samyarsadat/ROS-Remote/cad_files/solidworks_assets/parts/Generic_Power_Bank_Representation.SLDPRT

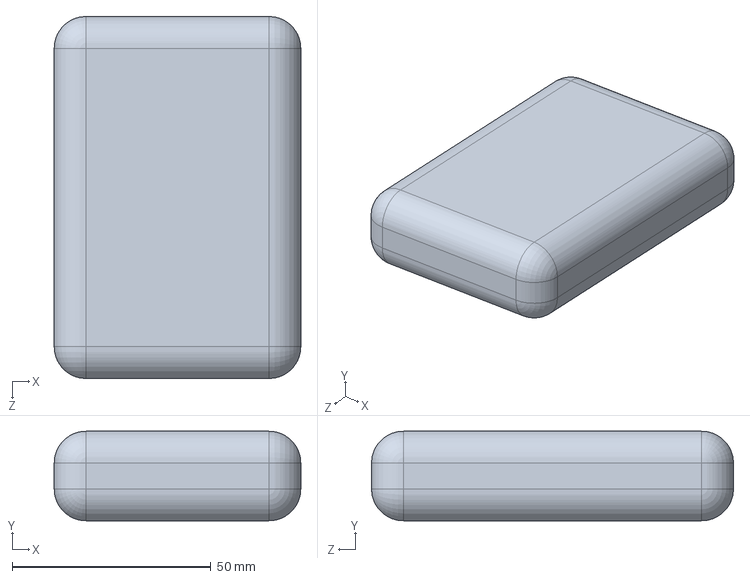
[picture p18: CAD file, 2026-08-17]
cad_files/solidworks_assets/parts/Generic_Power_Bank_Representation.SLDPRT
62.0 x 22.5 x 91.0 mm
