samyarsadat/ROS-Remote/cad_files/solidworks_assets/parts/40x60mm_protoboard.SLDPRT

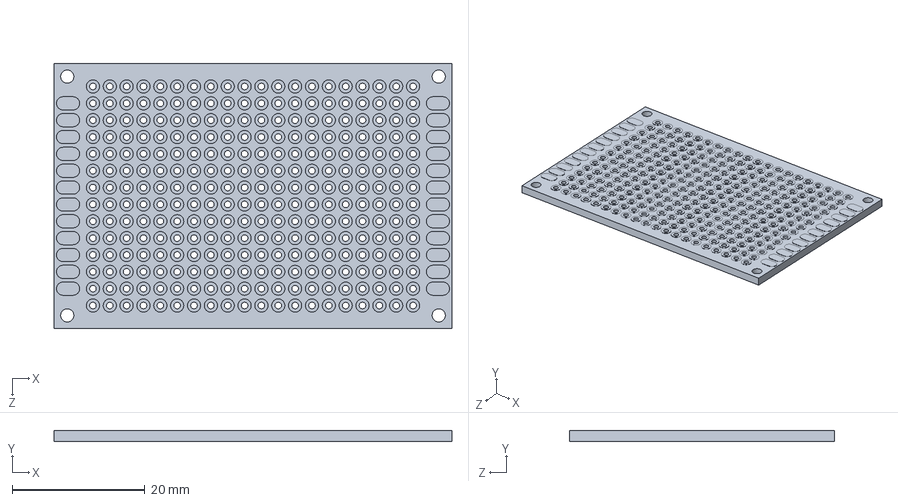
[picture p19: CAD file, 2026-08-17]
cad_files/solidworks_assets/parts/40x60mm_protoboard.SLDPRT
60.0 x 1.70 x 40.0 mm
