samyarsadat/ROS-Remote/cad_files/solidworks_assets/parts/Red_led.SLDPRT

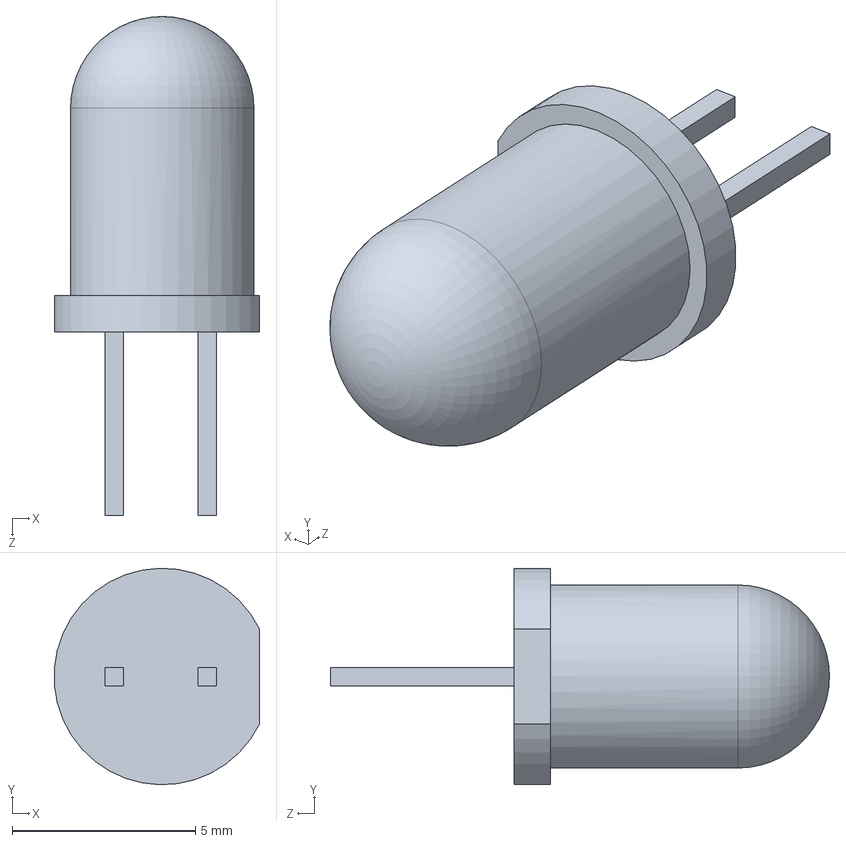
[picture p20: CAD file, 2026-08-17]
cad_files/solidworks_assets/parts/Red_led.SLDPRT
5.59 x 5.90 x 13.6 mm
