samyarsadat/ROS-Remote/cad_files/solidworks_assets/parts/7mm_Momentary_Button.SLDPRT

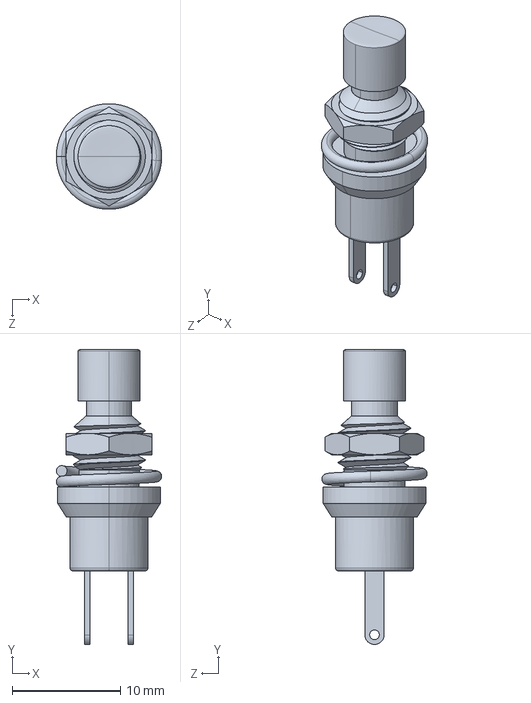
[picture p21: CAD file, 2026-08-17]
cad_files/solidworks_assets/parts/7mm_Momentary_Button.SLDPRT
9.76 x 27.3 x 9.76 mm
