samyarsadat/ROS-Remote/cad_files/solidworks_assets/parts/Raspberry_Pi_3.SLDPRT

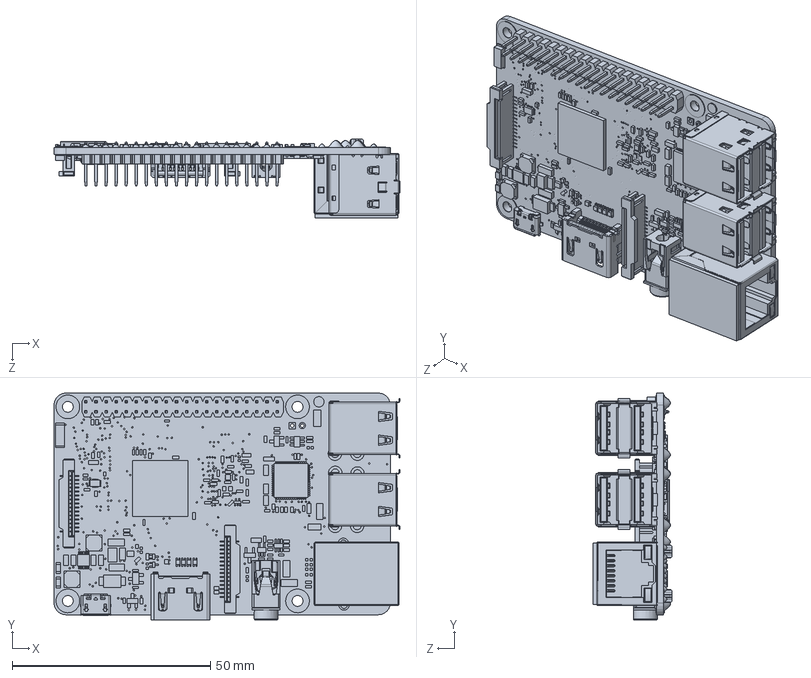
[picture p22: CAD file, 2026-08-17]
cad_files/solidworks_assets/parts/Raspberry_Pi_3.SLDPRT
87.4 x 57.3 x 19.9 mm
