samyarsadat/ROS-Remote/cad_files/solidworks_assets/parts/Potentiometer.sldprt

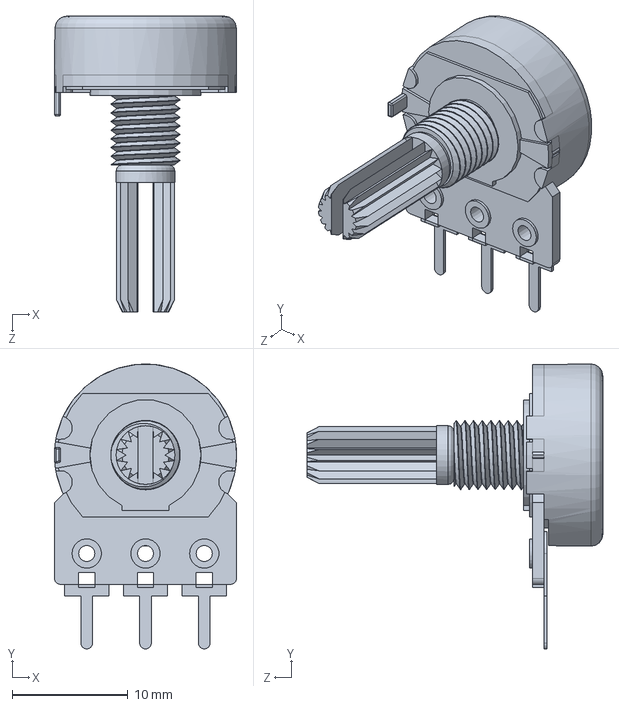
[picture p23: CAD file, 2026-08-17]
cad_files/solidworks_assets/parts/Potentiometer.sldprt
15.7 x 24.6 x 25.6 mm
