samyarsadat/ROS-Remote/cad_files/solidworks_assets/parts/M2.5_8.SLDPRT

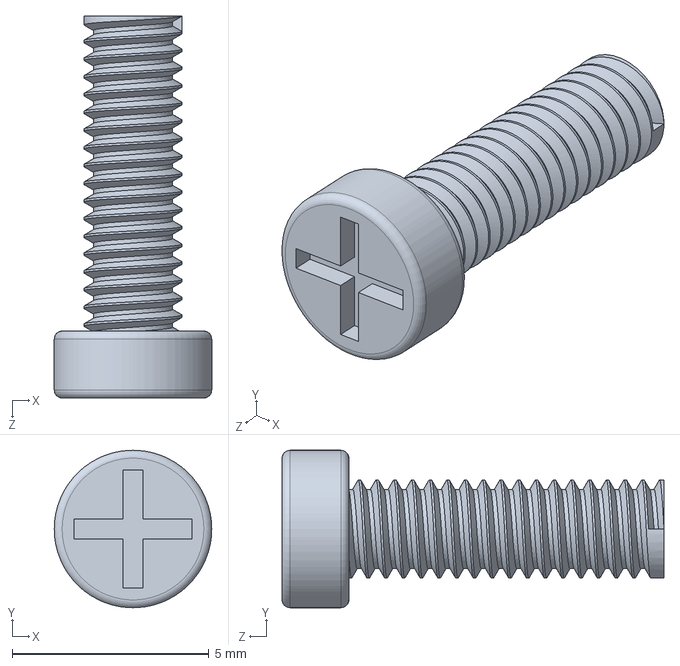
[picture p24: CAD file, 2026-08-17]
cad_files/solidworks_assets/parts/M2.5_8.SLDPRT
4.00 x 4.00 x 9.70 mm
