samyarsadat/ROS-Remote/cad_files/solidworks_assets/parts/16mm_e-stop_button.SLDPRT

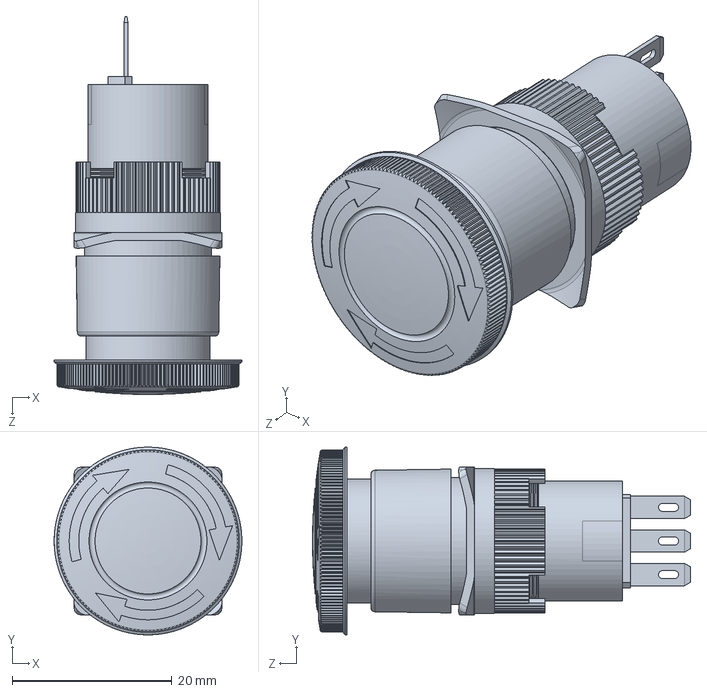
[picture p25: CAD file, 2026-08-17]
cad_files/solidworks_assets/parts/16mm_e-stop_button.SLDPRT
23.5 x 23.5 x 47.3 mm
