samyarsadat/ROS-Remote/cad_files/solidworks_assets/parts/Rotary_encoder_module.SLDPRT

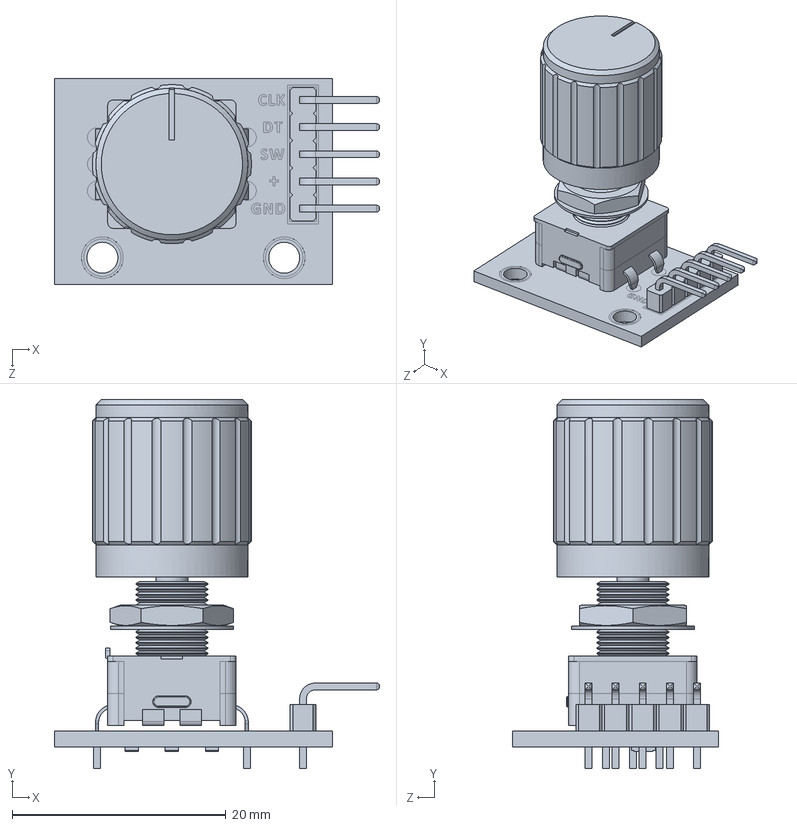
[picture p26: CAD file, 2026-08-17]
cad_files/solidworks_assets/parts/Rotary_encoder_module.SLDPRT
30.4 x 34.5 x 19.2 mm
