samyarsadat/ROS-Remote/cad_files/solidworks_assets/parts/20_pin_female_header_2.54mm.step

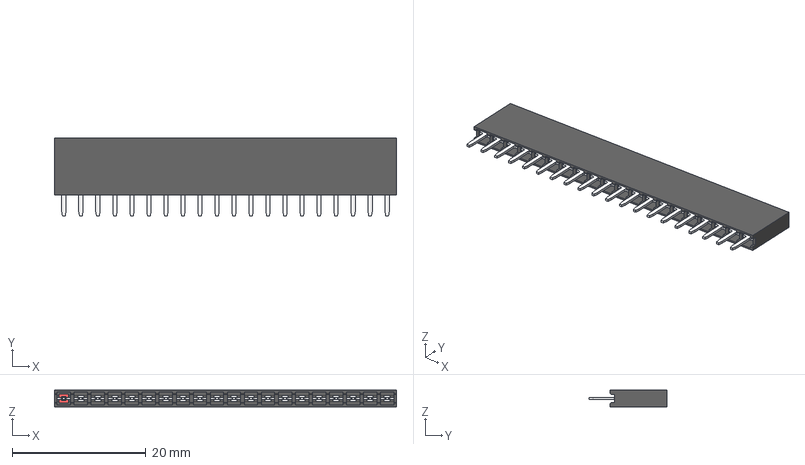
[picture p27: CAD file, 2024-07-23]
cad_files/solidworks_assets/parts/20_pin_female_header_2.54mm.step
51.0 x 11.7 x 2.50 mm
