samyarsadat/ROS-Remote/cad_files/solidworks_assets/parts/OM200A-M2_joystick.step

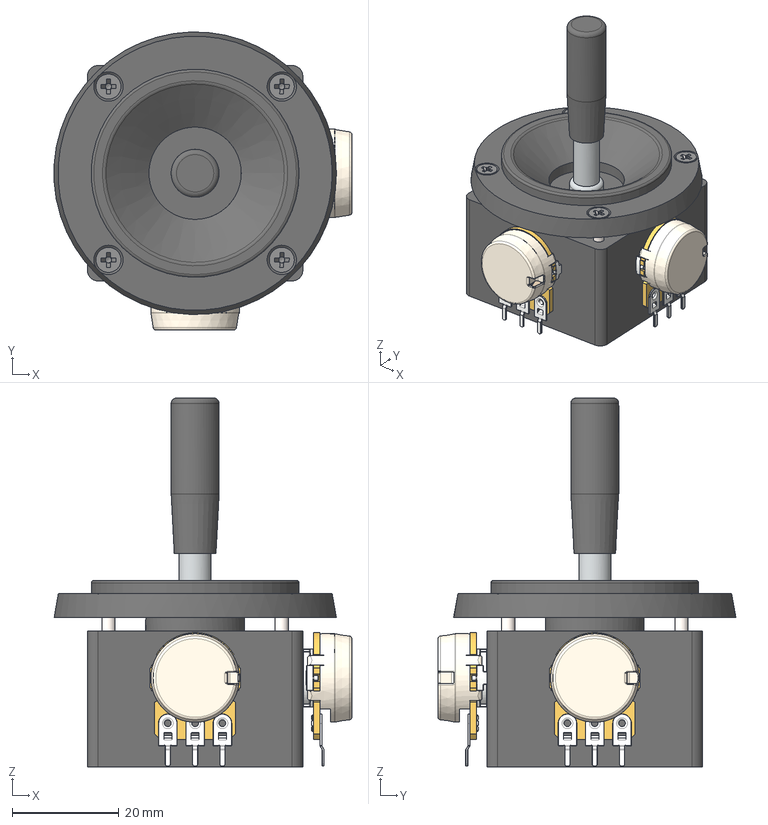
[picture p28: CAD file, 2024-07-23]
cad_files/solidworks_assets/parts/OM200A-M2_joystick.step
55.8 x 55.9 x 69.2 mm
Omter - 2 Axis potentiometer joystick without spring return OM200A-M2--1
pcb board x 2
base metal x 2
rotating rod metal x 2
pin1 x 6
sheild metal x 2
plastic base x 2
Mutter M7x075 x 2
Unterlegscheibe 11x7x0.5 x 2
Omter - 2 Axis potentiometer joystick without spring return OM200A-M2__
countersunk flat head cross recess screw_din x 4
