samyarsadat/ROS-Remote/cad_files/solidworks_assets/parts/12mm_key_operated_switch.step

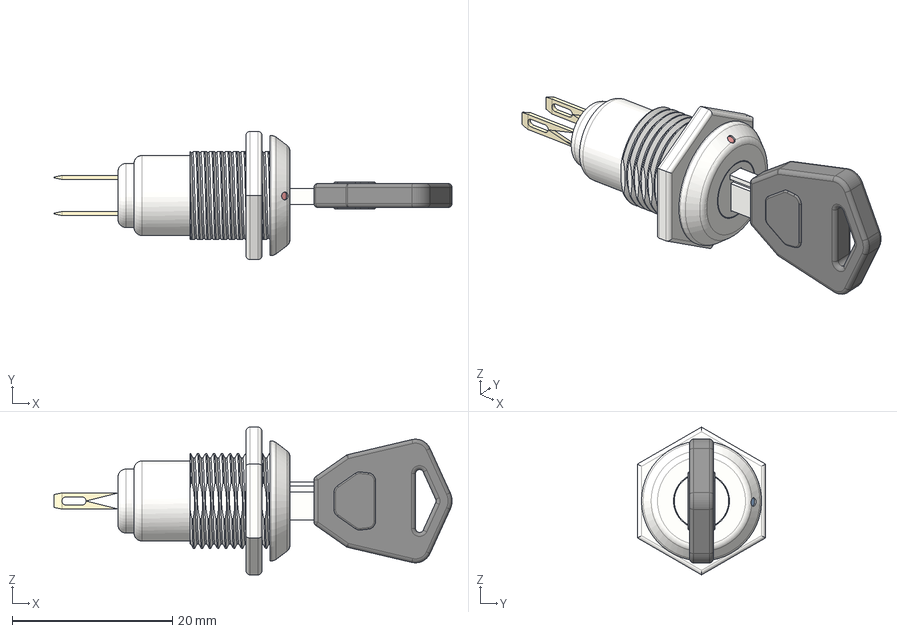
[picture p29: CAD file, 2024-07-23]
cad_files/solidworks_assets/parts/12mm_key_operated_switch.step
49.7 x 16.0 x 18.5 mm
