samyarsadat/ROS-Remote/cad_files/solidworks_assets/parts/20_pin_male_header_2.54mm.step

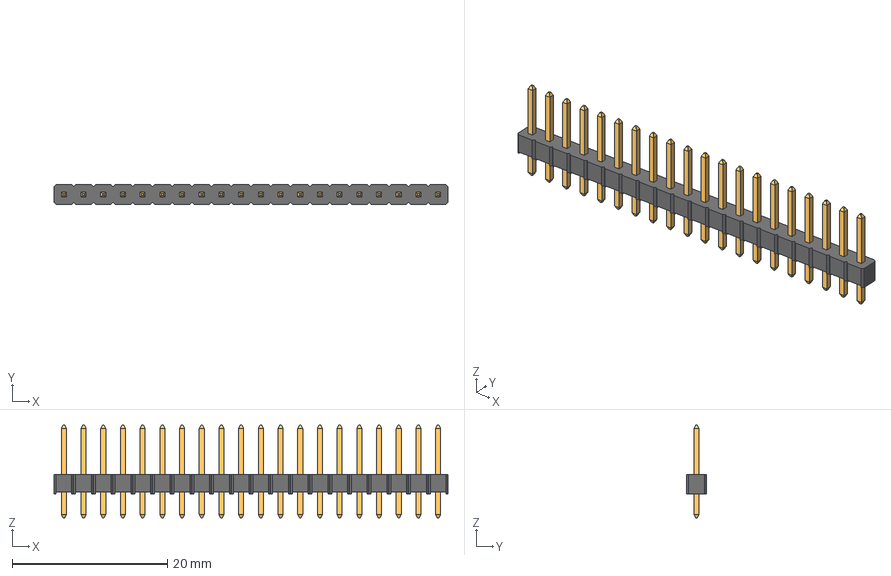
[picture p30: CAD file, 2024-07-23]
cad_files/solidworks_assets/parts/20_pin_male_header_2.54mm.step
50.8 x 2.54 x 11.9 mm
