samyarsadat/ROS-Remote/cad_files/solidworks_assets/parts/M2.5_20.SLDPRT

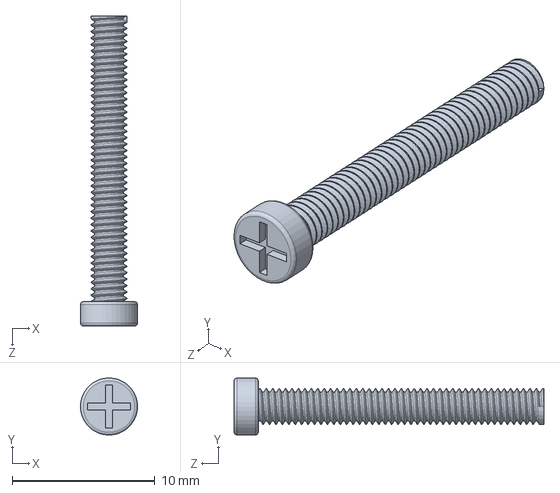
[picture p31: CAD file, 2024-07-19]
cad_files/solidworks_assets/parts/M2.5_20.SLDPRT
4.00 x 3.99 x 21.7 mm
