samyarsadat/ROS-Remote/cad_files/solidworks_assets/parts/Generic_DIN_7991.SLDPRT

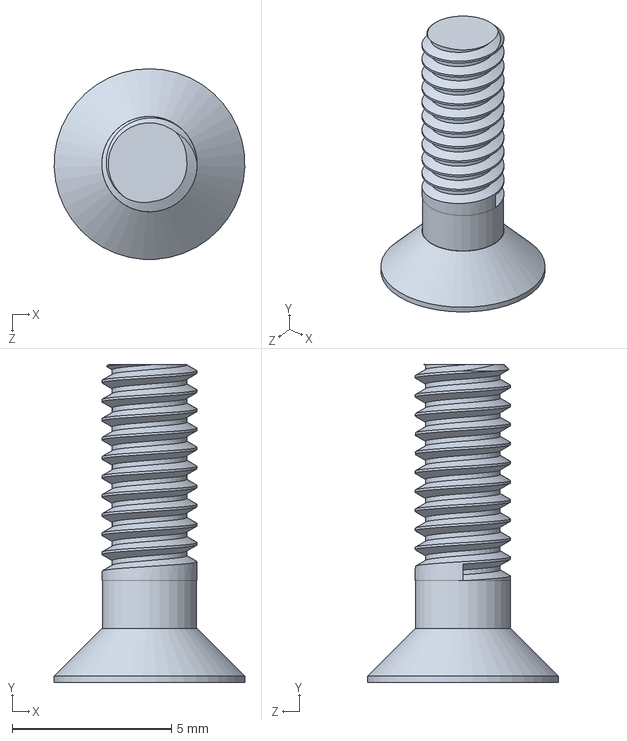
[picture p32: CAD file, 2024-07-19]
cad_files/solidworks_assets/parts/Generic_DIN_7991.SLDPRT
6.00 x 10.0 x 5.99 mm
