samyarsadat/ROS-Remote/cad_files/solidworks_assets/parts/Potentipmeter_knob.step

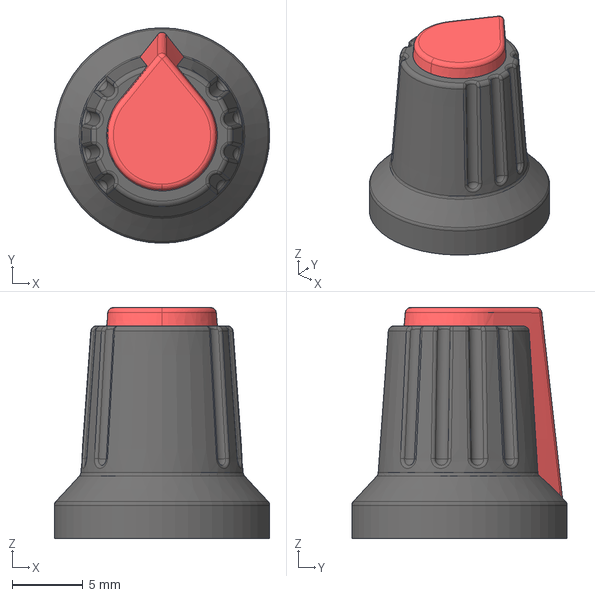
[picture p33: CAD file, 2024-07-19]
cad_files/solidworks_assets/parts/Potentipmeter_knob.step
15.2 x 15.2 x 16.3 mm
Rouge
Extérieur
