samyarsadat/ROS-Remote/source_code/ros_ws_remote/src/ros_remote_pui/ros_remote_pui/encoder_handler.py

#  The ROS remote project (PUI package)
#  Encoder IO handler. This is for GUI navigation using the encoder.
#  Copyright 2024 Samyar Sadat Akhavi
#  Written by Samyar Sadat Akhavi, 2024.
#
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
from PySide6.QtCore import QObject, Signal, QTimer, Slot
from PySide6.QtWidgets import QApplication, QPushButton, QTabBar, QCheckBox, QComboBox, QSlider, QWidget
from gpiozero import RotaryEncoder, Button
from ros_remote_gui.main_window import get_main_window
from ros_remote_pui.config import RpiIoConfig, ProgramConfig


# Encoder input handler
class EncoderInput(QObject):
    enc_rotated = Signal(bool)
    btn_pressed = Signal()

    def __init__(self):
        super().__init__()

        self._rotary_enc = RotaryEncoder(RpiIoConfig.ENCODER_PIN_A, RpiIoConfig.ENCODER_PIN_B)
        self._rotary_enc.when_rotated_clockwise = self._enc_rotate_call_cw
        self._rotary_enc.when_rotated_counter_clockwise = self._enc_rotate_call_ccw

        self._rotary_btn = Button(RpiIoConfig.ENCODER_BTN_PIN, pull_up=False, bounce_time=RpiIoConfig.BUTTON_DEBOUNCE_TIME_S)
        self._rotary_btn.when_activated = self._enc_btn_call

    def _enc_btn_call(self) -> None:
        self.btn_pressed.emit()

    def _enc_rotate_call_cw(self) -> None:
        self.enc_rotated.emit(True)

    def _enc_rotate_call_ccw(self) -> None:
        self.enc_rotated.emit(False)


# Encoder UI navigation handler
class EncoderNavHandler:
    def __init__(self):
        self._input_handler = EncoderInput()
        self._input_handler.enc_rotated.connect(self._enc_rotate)
        self._input_handler.btn_pressed.connect(self._enc_btn_press)

        self._highlight_timer = QTimer()
        self._highlight_timer.setInterval(ProgramConfig.ENCODER_HIGHLIGHT_TIMEOUT_MS)
        self._highlight_timer.setSingleShot(True)
        self._highlight_timer.timeout.connect(self._clear_highlight)

        self._highlight_stylesheet = "QWidget:focus { border: 1px solid blue; }"
        self._select_stylesheet = "QWidget:focus { border: 1px solid red; }"

        self._widget_selected = False
        self._selected_widget_name = ""

    @Slot()
    def _enc_btn_press(self) -> None:
        focused_widget = QApplication.focusWidget()
        self._check_selection_state(focused_widget)

        if isinstance(focused_widget, QPushButton):
            focused_widget.click()
        elif isinstance(focused_widget, QCheckBox):
            focused_widget.toggle()
        elif isinstance(focused_widget, QTabBar):
            current_index = focused_widget.currentIndex()
            next_index = (current_index + 1) % focused_widget.count()
            focused_widget.setCurrentIndex(next_index)
        elif isinstance(focused_widget, QComboBox):
            if not self._widget_selected:
                self._widget_selected = True
                self._selected_widget_name = focused_widget.objectName()

                if not focused_widget.view().isVisible():
                    focused_widget.showPopup()
                    focused_widget.setFocus()
            else:
                self._widget_selected = False
                self._selected_widget_name = ""

                if focused_widget.view().isVisible():
                    focused_widget.hidePopup()
                    focused_widget.setFocus()
        elif isinstance(focused_widget, QSlider):
            if not self._widget_selected:
                self._widget_selected = True
                self._selected_widget_name = focused_widget.objectName()
            else:
                self._widget_selected = False
                self._selected_widget_name = ""
        self._apply_highlight()

    @Slot(bool)
    def _enc_rotate(self, direction: bool) -> None:
        focused_widget = QApplication.focusWidget()
        self._check_selection_state(focused_widget)

        if isinstance(focused_widget, QComboBox) and self._widget_selected:
            current_index = focused_widget.currentIndex()
            if direction: next_index = (current_index + 1) % focused_widget.count()
            else: next_index = (current_index - 1) % focused_widget.count()
            focused_widget.setCurrentIndex(next_index)
        elif isinstance(focused_widget, QSlider) and self._widget_selected:
            new_value = focused_widget.value() + (focused_widget.singleStep() if direction else focused_widget.singleStep() * -1)
            focused_widget.setValue(new_value)
        else:
            if direction: get_main_window().focusNextChild()
            else: get_main_window().focusPreviousChild()
        self._apply_highlight()

    def _apply_highlight(self) -> None:
        if self._widget_selected and get_main_window().styleSheet() != self._select_stylesheet:
            get_main_window().setStyleSheet(self._select_stylesheet)
        elif (not self._widget_selected) and get_main_window().styleSheet() != self._highlight_stylesheet:
            get_main_window().setStyleSheet(self._highlight_stylesheet)

        if self._highlight_timer.isActive():
            self._highlight_timer.stop()
        self._highlight_timer.start()

    @staticmethod
    def _clear_highlight() -> None:
        get_main_window().setStyleSheet("")

    def _check_selection_state(self, focused_widget: QWidget) -> None:
        if self._selected_widget_name != "" and self._widget_selected and self._selected_widget_name != focused_widget.objectName():
            self._selected_widget_name = ""
            self._widget_selected = False
