samyarsadat/ROS-Remote/source_code/pico_ws/src/pico/config/tusb_config.h

/*
 * The MIT License (MIT)
 *
 * Copyright (c) 2019 Ha Thach (tinyusb.org)
 * Copyright (c) 2025 Samyar Sadat Akhavi
 *
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
 */

#pragma once


#ifdef __cplusplus
extern "C" {
#endif

//--------------------------------------------------------------------+
// Board Specific Configuration
//--------------------------------------------------------------------+

// RHPort number used for device can be defined by board.mk, default to port 0
#ifndef BOARD_TUD_RHPORT
#define BOARD_TUD_RHPORT      0
#endif

// RHPort max operational speed can defined by board.mk
#ifndef BOARD_TUD_MAX_SPEED
#define BOARD_TUD_MAX_SPEED   OPT_MODE_DEFAULT_SPEED
#endif

//--------------------------------------------------------------------
// COMMON CONFIGURATION
//--------------------------------------------------------------------

#ifndef CFG_TUSB_MCU
#error CFG_TUSB_MCU must be defined
#endif

#define CFG_TUSB_RHPORT0_MODE  OPT_MODE_DEVICE

#ifndef CFG_TUSB_OS
#define CFG_TUSB_OS            OPT_OS_PICO
#endif

#ifndef CFG_TUSB_DEBUG
#define CFG_TUSB_DEBUG         0
#endif

// Enable Device stack
#define CFG_TUD_ENABLED        1
#define CFG_TUD_MAX_SPEED      BOARD_TUD_MAX_SPEED

#ifndef CFG_TUSB_MEM_SECTION
#define CFG_TUSB_MEM_SECTION
#endif

#ifndef CFG_TUSB_MEM_ALIGN
#define CFG_TUSB_MEM_ALIGN     __attribute__ ((aligned(4)))
#endif

//--------------------------------------------------------------------
// DEVICE CONFIGURATION
//--------------------------------------------------------------------

#ifndef CFG_TUD_ENDPOINT0_SIZE
#define CFG_TUD_ENDPOINT0_SIZE   64
#endif

//------------- CLASS -------------//
#define CFG_TUD_HID              2
#define CFG_TUD_CDC              0
#define CFG_TUD_MSC              0
#define CFG_TUD_MIDI             0
#define CFG_TUD_VENDOR           0

// HID buffer size Should be sufficient to hold ID (if any) + Data
#define CFG_TUD_HID_EP_BUFSIZE   64

#ifdef __cplusplus
}
#endif
