samyarsadat/ROS-Remote/source_code/ros_ws_remote/src/ros_remote_hid/src/led_interface_node.cpp

/*
    The ROS remote project - Remote HID interface ROS package
    Copyright 2025 Samyar Sadat Akhavi.
    Written by Samyar Sadat Akhavi, 2025.

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
    You should have received a copy of the GNU General Public License
    along with this program.  If not, see <https://www.gnu.org/licenses/>.
*/

#include <cstdio>
#include <rclcpp/rclcpp.hpp>
#include "hid_helper.hpp"
#include "ros_remote_hid/srv/set_led_state.hpp"
#include "ros_remote_hid/srv/get_led_states.hpp"
#include <std_srvs/srv/trigger.hpp>
#include <rclcpp_components/register_node_macro.hpp>


#define DECLARE_PARAMETER(param_var_type, param_name, default_value, description_text)             \
    rcl_interfaces::msg::ParameterDescriptor param_descr_##param_name;                             \
    param_descr_##param_name.description = description_text;                                       \
    param_descr_##param_name.read_only = true;                                                     \
    param_name =                                                                                   \
        declare_parameter<param_var_type>(#param_name, default_value, param_descr_##param_name);


// Node class
class LEDInterfaceNode : public rclcpp::Node {
    public:
        explicit LEDInterfaceNode(const rclcpp::NodeOptions &options)
            : Node("led_interface_node", options) {
            RCLCPP_INFO(get_logger(), "LED HID interface node initializing...");

            // Parameters
            DECLARE_PARAMETER(uint16_t, vid, DEFAULT_VID, "Vendor ID of HID device");
            DECLARE_PARAMETER(uint16_t, pid, DEFAULT_PID, "Product ID of HID device");
            DECLARE_PARAMETER(uint8_t, itf_num, ITF_NUM_LEDS_HID, "Interface number of HID device");

            // Open HID device
            auto res = hid_device.open_hid(vid, pid, itf_num);
            if (!res) {
                throw std::runtime_error("Failed to open HID device: " + res.error());
            }

            // Callback groups
            multithread_cb_group = create_callback_group(rclcpp::CallbackGroupType::Reentrant);

            // Service servers
            set_led_state_service = create_service<ros_remote_hid::srv::SetLedState>(
                "set_led_state",
                std::bind(&LEDInterfaceNode::handle_set_led_state,
                          this,
                          std::placeholders::_1,
                          std::placeholders::_2),
                rclcpp::ServicesQoS(),
                multithread_cb_group);
            get_led_states_service = create_service<ros_remote_hid::srv::GetLedStates>(
                "get_led_states",
                std::bind(&LEDInterfaceNode::handle_get_led_states,
                          this,
                          std::placeholders::_1,
                          std::placeholders::_2),
                rclcpp::ServicesQoS(),
                multithread_cb_group);
            reopen_hid_device_service = create_service<std_srvs::srv::Trigger>(
                "reopen_hid_device",
                std::bind(&LEDInterfaceNode::handle_reopen_hid_device,
                          this,
                          std::placeholders::_1,
                          std::placeholders::_2));
        }

        ~LEDInterfaceNode() {
            hid_device.close_hid();
            RCLCPP_INFO(get_logger(), "LED HID interface node stopped.");
        }

    private:
        HIDDevice hid_device{get_logger()};

        uint16_t vid, pid;
        uint8_t itf_num;

        rclcpp::CallbackGroup::SharedPtr multithread_cb_group;
        rclcpp::Service<ros_remote_hid::srv::SetLedState>::SharedPtr set_led_state_service;
        rclcpp::Service<ros_remote_hid::srv::GetLedStates>::SharedPtr get_led_states_service;
        rclcpp::Service<std_srvs::srv::Trigger>::SharedPtr reopen_hid_device_service;

        // Callbacks
        void handle_set_led_state(
            const std::shared_ptr<ros_remote_hid::srv::SetLedState::Request> request,
            const std::shared_ptr<ros_remote_hid::srv::SetLedState::Response> response) {
            auto res =
                hid_device.set_led_state(request->index, request->led_mode, request->pwm_output);
            if (!res) {
                response->success = false;
                response->message = res.error();
                RCLCPP_ERROR_STREAM(get_logger(), "Failed to set LED state: " << res.error());
                return;
            }

            RCLCPP_DEBUG_STREAM(get_logger(),
                                "Set LED " << static_cast<int>(request->index) << " to mode "
                                           << static_cast<int>(request->led_mode)
                                           << " with PWM output " << request->pwm_output);

            response->success = true;
        }

        void handle_get_led_states(
            const std::shared_ptr<ros_remote_hid::srv::GetLedStates::Request> request,
            const std::shared_ptr<ros_remote_hid::srv::GetLedStates::Response> response) {
            (void) request;

            auto res = hid_device.get_led_states();
            if (!res) {
                response->success = false;
                response->message = res.error();
                RCLCPP_ERROR_STREAM(get_logger(), "Failed to get LED states: " << res.error());
                return;
            }

            for (size_t i = 0; i < NUMBER_OF_LEDS; i++) {
                response->led_mode[i] = res->mode[i];
                response->pwm_output[i] = res->pwm_out[i];
            }

            response->success = true;
        }

        void
        handle_reopen_hid_device(const std::shared_ptr<std_srvs::srv::Trigger::Request> request,
                                 const std::shared_ptr<std_srvs::srv::Trigger::Response> response) {
            (void) request;
            RCLCPP_WARN(get_logger(), "Reopening HID device...");

            hid_device.close_hid();
            auto res = hid_device.open_hid(vid, pid, itf_num);
            if (!res) {
                response->success = false;
                response->message = res.error();
                RCLCPP_ERROR_STREAM(get_logger(), "Failed to reopen HID device: " << res.error());
                return;
            }

            response->success = true;
        }
};


// Register the node class (composable node)
RCLCPP_COMPONENTS_REGISTER_NODE(LEDInterfaceNode)
