samyarsadat/ROS-Remote/source_code/ros_ws_remote/src/ros_remote_gui/ros_remote_gui/config.py

#  The ROS remote project (GUI package)
#  Program configuration
#  Copyright 2024-2025 Samyar Sadat Akhavi
#  Written by Samyar Sadat Akhavi, 2024-2025.
#
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
PROGRAM_VERSION = "25.9.7"
from rclpy.qos import QoSProfile, ReliabilityPolicy, HistoryPolicy, LivelinessPolicy


# ---- Program Info ----
class ProgramInfoConfig:
    VERSION = PROGRAM_VERSION
    VERSION_DATE = "2025-09-07 @ 12:39 UTC"

class ProgramConfig:
    THREADS_LIVELINESS_CHECK_INTERVAL_S = 2
    UI_DATA_UPDATE_INTERVAL_MS = 100
    UI_TIMER_STATE_UPDATE_INTERVAL_MS = 200
    VIEWPORT_TARGET_FPS = 25
    MAX_DIAG_MSG_HISTORY = 100
    STALE_DATA_TIMEOUT = 4   # 4s


# ---- ROS Config ----
class RosConfig:
    NODE_NAME = "remote_gui_node"
    NODE_NAMESPACE = ""
    EXECUTOR_DOMAIN_ID = None
    EXECUTOR_TIMEOUT = 0.05         # 50ms
    EXECUTOR_SHUTDOWN_TIMEOUT = 5   # 5s
    QOS_BEST_EFFORT = QoSProfile(reliability=ReliabilityPolicy.BEST_EFFORT, history=HistoryPolicy.KEEP_LAST, depth=1, liveliness=LivelinessPolicy.AUTOMATIC)
    QOS_RELIABLE = QoSProfile(reliability=ReliabilityPolicy.RELIABLE, history=HistoryPolicy.KEEP_LAST, depth=1, liveliness=LivelinessPolicy.AUTOMATIC)
    THREAD_NAME = "ros_thread"

class RosNames:
    ROBOT_NAMESPACE = "/ros_robot"

    CAMERA_FEED_TOPIC = f"{ROBOT_NAMESPACE}/cameras/front/image_raw/compressed"
    CAMERA_OVERLAY_TOPIC = f"{ROBOT_NAMESPACE}/cameras/front_overlay/image"

    DIAGNOSTICS_TOPIC = f"{ROBOT_NAMESPACE}/diagnostics"
    PING_DRIVER_TOPIC = f"{ROBOT_NAMESPACE}/diagnostics/ping_driver"
    ENABLE_RELAY_SRV = f"{ROBOT_NAMESPACE}/enable/set_relay"
    BATTERY_INFO_TOPIC = f"{ROBOT_NAMESPACE}/electrical/battery_state"
    ENCODER_ODOM_TOPIC = f"{ROBOT_NAMESPACE}/pos_data/encoder_odom"
    SET_CAMERA_LEDS_SRV = f"{ROBOT_NAMESPACE}/lights/camera/set"
    GET_CAMERA_LEDS_SRV = f"{ROBOT_NAMESPACE}/lights/camera/get"
    IMU_SENS_TOPIC = f"{ROBOT_NAMESPACE}/pos_data/imu"
    ENV_TEMP_SENS_TOPIC = f"{ROBOT_NAMESPACE}/env_sensors/temp"
    ENV_HUMIDITY_SENS_TOPIC = f"{ROBOT_NAMESPACE}/env_sensors/humidity"
    EMERGENCY_STOP_TOPIC = f"{ROBOT_NAMESPACE}/emergency_stop"
    PICO_A_CPU_TEMP_TOPIC = f"{ROBOT_NAMESPACE}/sys_temps/processor/pico_a"
    PICO_B_CPU_TEMP_TOPIC = f"{ROBOT_NAMESPACE}/sys_temps/processor/pico_b"
    PICO_A_SELFTEST_SRV = f"{ROBOT_NAMESPACE}/self_test/run_pico_a_routines"
    PICO_B_SELFTEST_SRV = f"{ROBOT_NAMESPACE}/self_test/run_pico_b_routines"
    PICO_A_CALIBRATE_SRV = f"{ROBOT_NAMESPACE}/calibrate/run_pico_a_routines"
    ENABLE_EMITTERS_SRV = f"{ROBOT_NAMESPACE}/enable/set_emitters"
    GET_EMITTERS_ENABLED_SRV = f"{ROBOT_NAMESPACE}/enable/get_emitters"
    LEFT_MTR_CTRL_TOPIC = f"{ROBOT_NAMESPACE}/motors/controllers/left_state"
    RIGHT_MTR_CTRL_TOPIC = f"{ROBOT_NAMESPACE}/motors/controllers/right_state"
    MTR_CTRL_ENABLE_SRV = f"{ROBOT_NAMESPACE}/motors/controllers/enable"
    MTR_CTRL_SET_PID_SRV = f"{ROBOT_NAMESPACE}/motors/controllers/set_pid"

    MICRO_SWITCH_TOPIC_BASE = ROBOT_NAMESPACE + "/range_sens/micro_switch/{}"
    MICRO_SWITCH_TOPIC_NAMES = ["front_right", "front_left", "back_right", "back_left"]

    ULTRASONIC_SENS_TOPIC_BASE = ROBOT_NAMESPACE + "/range_sens/ultrasonic/{}"
    ULTRASONIC_SENS_TOPIC_NAMES = ["front", "back", "right", "left"]

    CLIFF_SENS_TOPIC_BASE = ROBOT_NAMESPACE + "/range_sens/cliff/{}"
    CLIFF_SENS_TOPIC_NAMES = ["front_{i}".format(i=i) for i in range(1, 5)] + ["back_{i}".format(i=i) for i in range(1, 5)]

class RosFrameIds:
    CLIFF_SENS_FRAME_IDS = ["f{i}".format(i=i) for i in range(1, 5)] + ["b{i}".format(i=i) for i in range(1, 5)]
    CLIFF_SENS_BASE_FRAME_ID = "{}_cliff_sens_link"
    ULTRASONIC_SENS_BASE_FRAME_ID = "{}_ultrasonic_emit_link"
    MICRO_SW_SENS_BASE_FRAME_ID = "{}_microswitch_link"
