samyarsadat/ROS-Remote/source_code/ros_ws_remote/src/ros_remote_gui/ros_remote_gui/main.py

#  The ROS remote project (GUI package)
#  Main file - everything is ran from here
#  Copyright 2024 Samyar Sadat Akhavi
#  Written by Samyar Sadat Akhavi, 2024.
#
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
import sys
import threading
from PySide6.QtWidgets import QApplication
from PySide6.QtCore import QProcess, QTimer
from ros_remote_gui.config import ProgramConfig, RosConfig


# ---- QT application ----
qt_app = QApplication(sys.argv)
from ros_remote_gui.main_window import get_main_window   # Must import main_window after qt_app init!


def main():
    from ros_remote_gui.ros_main import ros_executor_thread, is_ros_node_initialized, get_ros_node
    from ros_remote_pui.remote_state import init_remote_state
    get_main_window().init_ui_handlers()
    init_remote_state()

    # Start the ROS thread
    stop_ros_thread = False
    ros_thread = threading.Thread(target=ros_executor_thread, args=(lambda: stop_ros_thread, ), name=RosConfig.THREAD_NAME)
    ros_thread.start()

    # Create a timer for checking ROS thread liveliness
    def ros_liveliness_check() -> None:
        if not ros_thread.is_alive():
            if is_ros_node_initialized():
                get_ros_node().get_logger().fatal("The ROS thread has died! Terminating program.")
            else:
                print("The ROS thread has died! Terminating program.")
            QApplication.exit(1)

    ros_liveliness_timer = QTimer()
    ros_liveliness_timer.timeout.connect(ros_liveliness_check)
    ros_liveliness_timer.start(ProgramConfig.THREADS_LIVELINESS_CHECK_INTERVAL_S * 1000)

    # Start the application
    get_main_window().show()
    qt_ret_code = QApplication.exec()

    # Shutdown
    stop_ros_thread = True
    ros_thread.join()

    if is_ros_node_initialized():
        get_ros_node().get_logger().info(f"Program exiting with code {qt_ret_code}")

    if get_main_window().restart_on_quit:
        qt_app_args = QApplication.arguments(); qt_app_args.pop(0)
        QProcess.startDetached(QApplication.arguments()[0], qt_app_args)

    sys.exit(qt_ret_code)
